TMRh20/FeatherAudio/Examples/PDM_Receiver/PDM_Receiver.ino

/* Example of receiving audio over radio and playing it back.
 *
 */ 

#include <AutoAnalogAudio.h>
#include <nrf_to_nrf.h>

AutoAnalog aaAudio;
nrf_to_nrf radio;

uint8_t address[][6] = { "1Node", "2Node" };
#define BUFFER_SIZE 124

void setup() {

  Serial.begin(115200);

  radio.begin();
  radio.setChannel(50);
  radio.setPayloadSize(BUFFER_SIZE);
  radio.setAutoAck(0);
  radio.setDataRate(NRF_2MBPS);
  radio.openReadingPipe(1,address[1]);
  radio.startListening();

  Serial.println("Analog Audio Begin");
  aaAudio.I2S_PIN_SCK = 3; //BCLK
  aaAudio.I2S_PIN_LRCK = 28; //WS
  aaAudio.begin(0, 2);  //Setup aaAudio using I2S output

  //Setup for audio: Use 16-bit, mono WAV files @ 32kHz
  aaAudio.dacBitsPerSample = 16;    // 16-bit
  aaAudio.setSampleRate(32000, 0); // 32khz, mono


}

void loop() {
  
  if(radio.available()){
    radio.read(&aaAudio.dacBuffer16[0],BUFFER_SIZE);
    aaAudio.feedDAC(0,BUFFER_SIZE/2);
  }

}
